proboterror/Loewe_VGA_Module_Q2500/doc/Q2500-H/S88176B_H050+053-056.pdf

# 47n 680R 680R

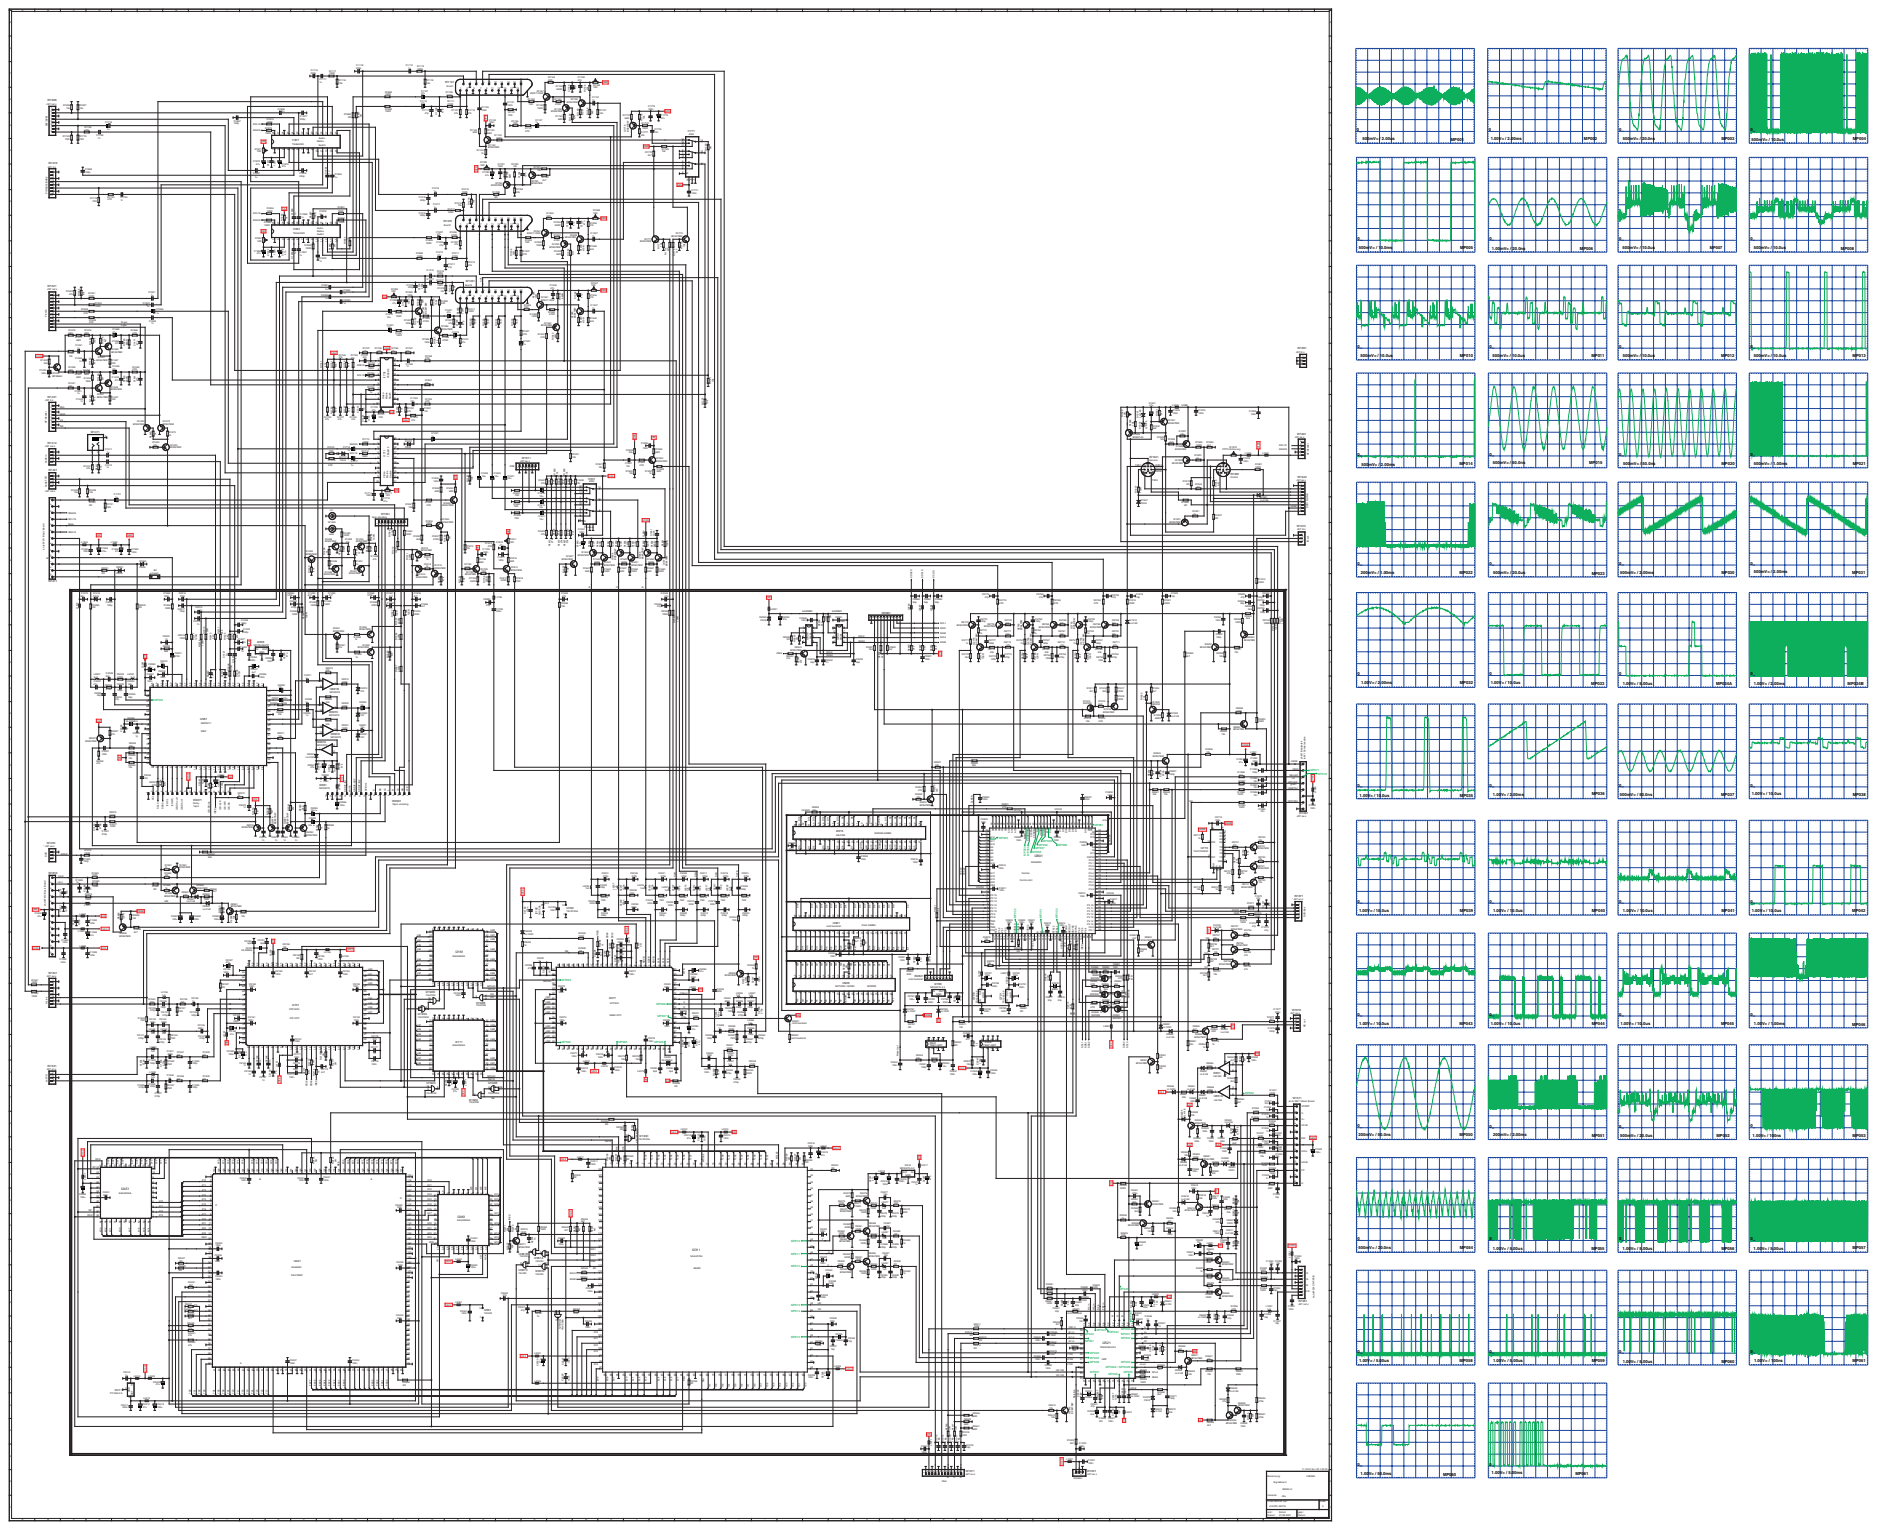
[picture p19: page 1]

an TVO Audio TVO Audio in Frontb. PIP/SAT2/DVB2 SAT/DVB1

HF-Sender JST nat s

an,to W610 Basic Board

RC out DVD-Bus

an,to W511 Basic Board LM 358

Code-Teile-Nr. Lpl.: | Index

erst.: Simon Datum: 27.08.2001 | gepr.: Datum:
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
